Nebu0528/28-Pins-Arduino/3D Component Models/m20-7820842_asm.stp

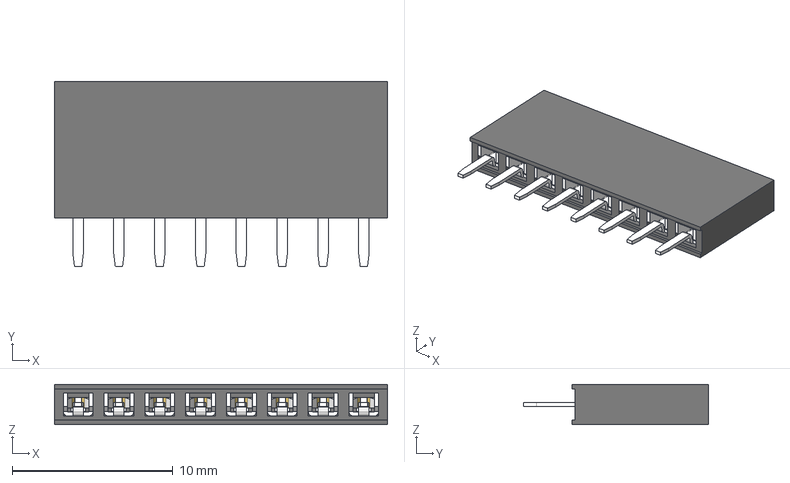
[picture p15: CAD file, 2022-02-19]
3D Component Models/m20-7820842_asm.stp
20.7 x 11.5 x 2.50 mm
M20-78208_MOULD
M20-782_CONTACT x 8
