Nebu0528/28-Pins-Arduino/3D Component Models/m20-7820646_asm.stp

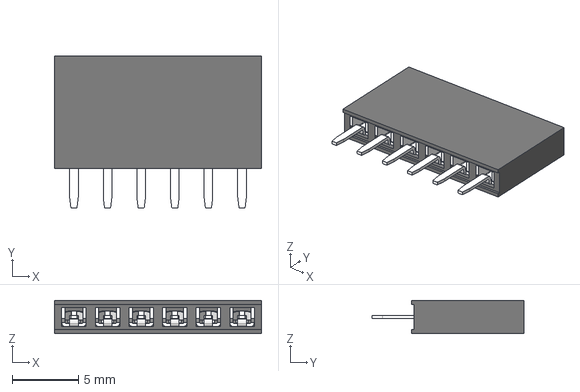
[picture p16: CAD file, 2022-02-19]
3D Component Models/m20-7820646_asm.stp
15.6 x 11.5 x 2.50 mm
M20-78206_MOULD
M20-782_CONTACT x 6
