Nebu0528/28-Pins-Arduino/3D Component Models/m20-7821046_asm.stp

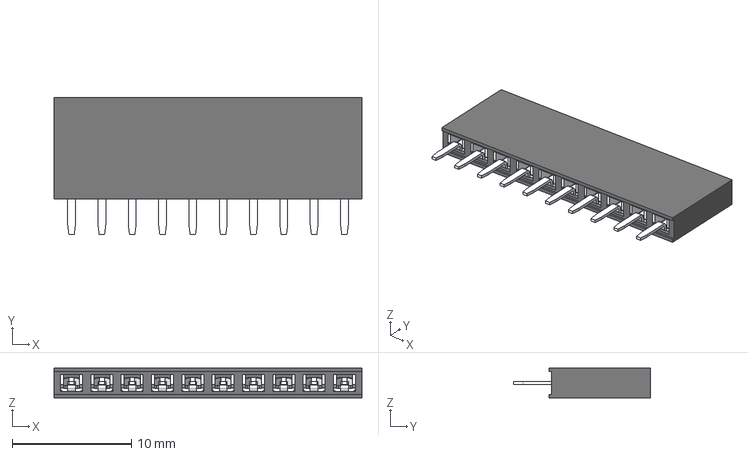
[picture p17: CAD file, 2022-02-19]
3D Component Models/m20-7821046_asm.stp
25.8 x 11.5 x 2.50 mm
M20-78210_MOULD
M20-782_CONTACT x 10
