Nebu0528/28-Pins-Arduino/3D Component Models/TPS73701DCQ.step

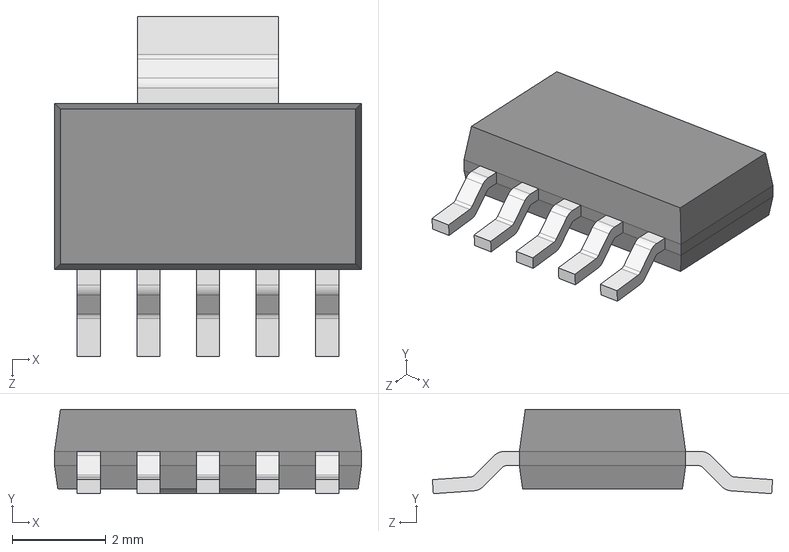
[picture p18: CAD file, 2022-02-19]
3D Component Models/TPS73701DCQ.step
6.55 x 1.80 x 7.26 mm
